Elecrow-RD/2-PACK-2.4inch-ESP32-Solo-Miner-LCD-Display/example/V1.0_A_green_circular_sticker_on_the_back/IDF_Code/DHT_screen_2.4_base/components/lvgl-3/docs/_static/img/js_calculator.gif

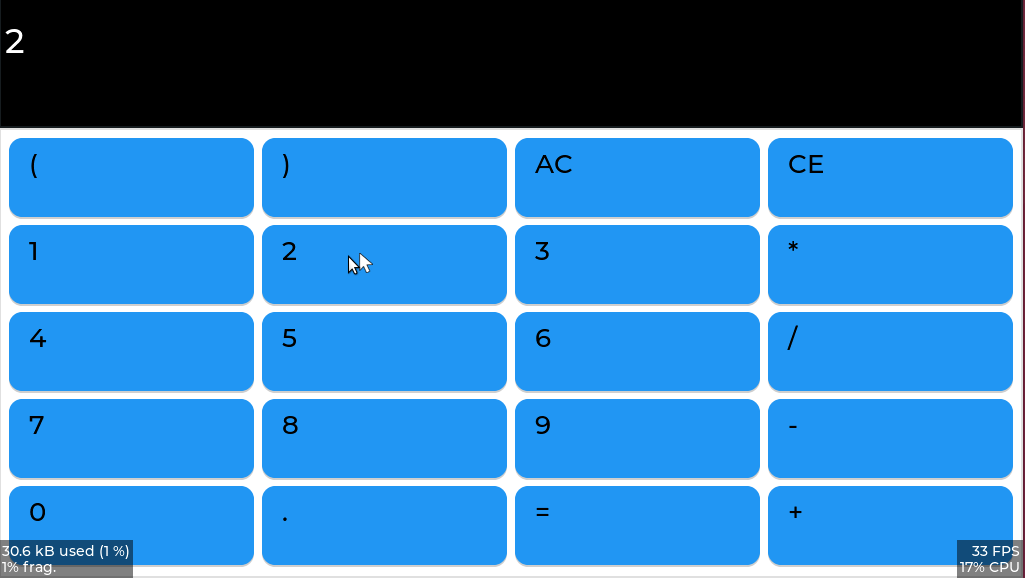
example/V1.0_A_green_circular_sticker_on_the_back/IDF_Code/DHT_screen_2.4_base/components/lvgl-3/docs/_static/img/js_calculator.gif
