Elecrow-RD/2-PACK-2.4inch-ESP32-Solo-Miner-LCD-Display/example/V1.0_A_green_circular_sticker_on_the_back/IDF_Code/DHT_screen_2.4_base/components/TFT_eSPI/examples/320 x 240/All_Free_Fonts_Demo/All_Free_Fonts_Demo.ino

/*
  Example for TFT_eSPI library

  Created by Bodmer 31/12/16

  This example draws all fonts (as used by the Adafruit_GFX library) onto the
  screen. These fonts are called the GFX Free Fonts (GFXFF) in this library.

  The fonts are referenced by a short name, see the Free_Fonts.h file
  attached to this sketch.

  Other True Type fonts could be converted using the utility within the
  "fontconvert" folder inside the library. This converted has also been
  copied from the Adafruit_GFX library. 

  Since these fonts are a recent addition Adafruit do not have a tutorial
  available yet on how to use the fontconvert utility.   Linux users will
  no doubt figure it out!  In the meantime there are 48 font files to use
  in sizes from 9 point to 24 point, and in normal, bold, and italic or
  oblique styles.

  This example sketch uses both the print class and drawString() functions
  to plot text to the screen.

  Make sure LOAD_GFXFF is defined in the User_Setup.h file within the
  library folder.

  --------------------------- NOTE ----------------------------------------
  The free font encoding format does not lend itself easily to plotting
  the background without flicker. For values that changes on screen it is
  better to use Fonts 1- 8 which are encoded specifically for rapid
  drawing with background.
  -------------------------------------------------------------------------

  #########################################################################
  ###### DON'T FORGET TO UPDATE THE User_Setup.h FILE IN THE LIBRARY ######
  ######       TO SELECT YOUR DISPLAY TYPE AND ENABLE FONTS          ######
  #########################################################################
*/

#define TEXT "aA MWyz~12" // Text that will be printed on screen in any font

#include "Free_Fonts.h" // Include the header file attached to this sketch

#include "SPI.h"
#include "TFT_eSPI.h"

// Use hardware SPI
TFT_eSPI tft = TFT_eSPI();

unsigned long drawTime = 0;

void setup(void) {

  tft.begin();

  tft.setRotation(1);

}

void loop() {

  // >>>>>>>>>>>>>>>>>>>>>>>>>>>>>>>>>>>>>>>>>>>>>>>>>>>>>>>>>>>>>>>>>>>>>>>>>>>>>>>>>
  // Show all 48 fonts in centre of screen ( x,y coordinate 160,120)
  // >>>>>>>>>>>>>>>>>>>>>>>>>>>>>>>>>>>>>>>>>>>>>>>>>>>>>>>>>>>>>>>>>>>>>>>>>>>>>>>>>

  // Where font sizes increase the screen is not cleared as the larger fonts overwrite
  // the smaller one with the background colour.

  // Set text datum to middle centre
  tft.setTextDatum(MC_DATUM);

  // Set text colour to orange with black background
  tft.setTextColor(TFT_WHITE, TFT_BLACK);
  
  tft.fillScreen(TFT_BLACK);            // Clear screen
  tft.setFreeFont(FF18);                 // Select the font
  tft.drawString(sFF1, 160, 60, GFXFF);// Print the string name of the font
  tft.setFreeFont(FF1);                 // Select the font
  tft.drawString(TEXT, 160, 120, GFXFF);// Print the string name of the font
  delay(1000);
  //tft.fillScreen(TFT_BLACK);
  tft.setFreeFont(FF18);                 // Select the font
  tft.drawString(sFF2, 160, 60, GFXFF);// Print the string name of the font
  tft.setFreeFont(FF2);
  tft.drawString(TEXT, 160, 120, GFXFF);
  delay(1000);
  //tft.fillScreen(TFT_BLACK);
  tft.setFreeFont(FF18);                 // Select the font
  tft.drawString(sFF3, 160, 60, GFXFF);// Print the string name of the font
  tft.setFreeFont(FF3);
  tft.drawString(TEXT, 160, 120, GFXFF);
  delay(1000);
  //tft.fillScreen(TFT_BLACK);
  tft.setFreeFont(FF18);                 // Select the font
  tft.drawString(sFF4, 160, 60, GFXFF);// Print the string name of the font
  tft.setFreeFont(FF4);
  tft.drawString(TEXT, 160, 120, GFXFF);
  delay(1000);
  
  tft.fillScreen(TFT_BLACK);
  tft.setFreeFont(FF18);                 // Select the font
  tft.drawString(sFF5, 160, 60, GFXFF);// Print the string name of the font
  tft.setFreeFont(FF5);
  tft.drawString(TEXT, 160, 120, GFXFF);
  delay(1000);
  //tft.fillScreen(TFT_BLACK);
  tft.setFreeFont(FF18);                 // Select the font
  tft.drawString(sFF6, 160, 60, GFXFF);// Print the string name of the font
  tft.setFreeFont(FF6);
  tft.drawString(TEXT, 160, 120, GFXFF);
  delay(1000);
  //tft.fillScreen(TFT_BLACK);
  tft.setFreeFont(FF18);                 // Select the font
  tft.drawString(sFF7, 160, 60, GFXFF);// Print the string name of the font
  tft.setFreeFont(FF7);
  tft.drawString(TEXT, 160, 120, GFXFF);
  delay(1000);
  //tft.fillScreen(TFT_BLACK);
  tft.setFreeFont(FF18);                 // Select the font
  tft.drawString(sFF8, 160, 60, GFXFF);// Print the string name of the font
  tft.setFreeFont(FF8);
  tft.drawString(TEXT, 160, 120, GFXFF);
  delay(1000);
  
  tft.fillScreen(TFT_BLACK);
  tft.setFreeFont(FF18);                 // Select the font
  tft.drawString(sFF9, 160, 60, GFXFF);// Print the string name of the font
  tft.setFreeFont(FF9);
  tft.drawString(TEXT, 160, 120, GFXFF);
  delay(1000);
  //tft.fillScreen(TFT_BLACK);
  tft.setFreeFont(FF18);                 // Select the font
  tft.drawString(sFF10, 160, 60, GFXFF);// Print the string name of the font
  tft.setFreeFont(FF10);
  tft.drawString(TEXT, 160, 120, GFXFF);
  delay(1000);
  //tft.fillScreen(TFT_BLACK);
  tft.setFreeFont(FF18);                 // Select the font
  tft.drawString(sFF11, 160, 60, GFXFF);// Print the string name of the font
  tft.setFreeFont(FF11);
  tft.drawString(TEXT, 160, 120, GFXFF);
  delay(1000);
  //tft.fillScreen(TFT_BLACK);
  tft.setFreeFont(FF18);                 // Select the font
  tft.drawString(sFF12, 160, 60, GFXFF);// Print the string name of the font
  tft.setFreeFont(FF12);
    tft.drawString(TEXT, 160, 120, GFXFF);
  delay(1000);
  
  tft.fillScreen(TFT_BLACK);
  tft.setFreeFont(FF18);                 // Select the font
  tft.drawString(sFF13, 160, 60, GFXFF);// Print the string name of the font
  tft.setFreeFont(FF13);
  tft.drawString(TEXT, 160, 120, GFXFF);
  delay(1000);
  //tft.fillScreen(TFT_BLACK);
  tft.setFreeFont(FF18);                 // Select the font
  tft.drawString(sFF14, 160, 60, GFXFF);// Print the string name of the font
  tft.setFreeFont(FF14);
  tft.drawString(TEXT, 160, 120, GFXFF);
  delay(1000);
  //tft.fillScreen(TFT_BLACK);
  tft.setFreeFont(FF18);                 // Select the font
  tft.drawString(sFF15, 160, 60, GFXFF);// Print the string name of the font
  tft.setFreeFont(FF15);
  tft.drawString(TEXT, 160, 120, GFXFF);
  delay(1000);
  //tft.fillScreen(TFT_BLACK);
  tft.setFreeFont(FF18);                 // Select the font
  tft.drawString(sFF16, 160, 60, GFXFF);// Print the string name of the font
  tft.setFreeFont(FF16);
    tft.drawString(TEXT, 160, 120, GFXFF);
  delay(1000);
  
  tft.fillScreen(TFT_BLACK);
  tft.setFreeFont(FF18);                 // Select the font
  tft.drawString(sFF17, 160, 60, GFXFF);// Print the string name of the font
  tft.setFreeFont(FF17);
  tft.drawString(TEXT, 160, 120, GFXFF);
  delay(1000);
  //tft.fillScreen(TFT_BLACK);
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
  delay(1000);
  //tft.fillScreen(TFT_BLACK);
  tft.setFreeFont(FF18);                 // Select the font
  tft.drawString(sFF47, 160, 60, GFXFF);// Print the string name of the font
  tft.setFreeFont(FF47);
  tft.drawString(TEXT, 160, 120, GFXFF);
  delay(1000);
  //tft.fillScreen(TFT_BLACK);
  tft.setFreeFont(FF18);                 // Select the font
  tft.drawString(sFF48, 160, 60, GFXFF);// Print the string name of the font
  tft.setFreeFont(FF48);
  tft.drawString(TEXT, 160, 120, GFXFF);
  delay(1000);

}

// There follows a crude way of flagging that this example sketch needs fonts which
// have not been enbabled in the User_Setup.h file inside the TFT_HX8357 library.
//
// These lines produce errors during compile time if settings in User_Setup are not correct
//
// The error will be "does not name a type" but ignore this and read the text between ''
// it will indicate which font or feature needs to be enabled
//
// Either delete all the following lines if you do not want warnings, or change the lines
// to suit your sketch modifications.

#ifndef LOAD_GLCD
//ERROR_Please_enable_LOAD_GLCD_in_User_Setup
#endif

#ifndef LOAD_GFXFF
ERROR_Please_enable_LOAD_GFXFF_in_User_Setup!
#endif
