Elecrow-RD/2-PACK-2.4inch-ESP32-Solo-Miner-LCD-Display/example/V1.0_A_green_circular_sticker_on_the_back/IDF_Code/DHT_screen_2.4_base/components/arduino-esp32-master/cores/esp32/HardwareSerial.h

/*
 HardwareSerial.h - Hardware serial library for Wiring
 Copyright (c) 2006 Nicholas Zambetti.  All right reserved.

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
 Modified 28 September 2010 by Mark Sproul
 Modified 14 August 2012 by Alarus
 Modified 3 December 2013 by Matthijs Kooijman
 Modified 18 December 2014 by Ivan Grokhotkov (esp8266 platform support)
 Modified 31 March 2015 by Markus Sattler (rewrite the code for UART0 + UART1 support in ESP8266)
 Modified 25 April 2015 by Thomas Flayols (add configuration different from 8N1 in ESP8266)
 Modified 13 October 2018 by Jeroen Döll (add baudrate detection)
 Baudrate detection example usage (detection on Serial1):
   void setup() {
     Serial.begin(115200);
     delay(100);
     Serial.println();

     Serial1.begin(0, SERIAL_8N1, -1, -1, true, 11000UL);  // Passing 0 for baudrate to detect it, the last parameter is a timeout in ms

     unsigned long detectedBaudRate = Serial1.baudRate();
     if(detectedBaudRate) {
       Serial.printf("Detected baudrate is %lu\n", detectedBaudRate);
     } else {
       Serial.println("No baudrate detected, Serial1 will not work!");
     }
   }

 Pay attention: the baudrate returned by baudRate() may be rounded, eg 115200 returns 115201
 */

#ifndef HardwareSerial_h
#define HardwareSerial_h

#include <inttypes.h>
#include <functional>
#include "Stream.h"
#include "esp32-hal.h"
#include "soc/soc_caps.h"
#include "HWCDC.h"

#include "freertos/FreeRTOS.h"
#include "freertos/task.h"
#include "freertos/semphr.h"

typedef enum {
    UART_BREAK_ERROR,
    UART_BUFFER_FULL_ERROR,
    UART_FIFO_OVF_ERROR,
    UART_FRAME_ERROR,
    UART_PARITY_ERROR
} hardwareSerial_error_t;

typedef std::function<void(void)> OnReceiveCb;
typedef std::function<void(hardwareSerial_error_t)> OnReceiveErrorCb;

class HardwareSerial: public Stream
{
public:
    HardwareSerial(int uart_nr);
    ~HardwareSerial();

    // setRxTimeout sets the timeout after which onReceive callback will be called (after receiving data, it waits for this time of UART rx inactivity to call the callback fnc)
    // param symbols_timeout defines a timeout threshold in uart symbol periods. Setting 0 symbol timeout disables the callback call by timeout.
    //                       Maximum timeout setting is calculacted automatically by IDF. If set above the maximum, it is ignored and an error is printed on Serial0 (check console).
    //                       Examples: Maximum for 11 bits symbol is 92 (SERIAL_8N2, SERIAL_8E1, SERIAL_8O1, etc), Maximum for 10 bits symbol is 101 (SERIAL_8N1).
    //                       For example symbols_timeout=1 defines a timeout equal to transmission time of one symbol (~11 bit) on current baudrate. 
    //                       For a baudrate of 9600, SERIAL_8N1 (10 bit symbol) and symbols_timeout = 3, the timeout would be 3 / (9600 / 10) = 3.125 ms
    void setRxTimeout(uint8_t symbols_timeout);

    // onReceive will setup a callback that will be called whenever an UART interruption occurs (UART_INTR_RXFIFO_FULL or UART_INTR_RXFIFO_TOUT)
    // UART_INTR_RXFIFO_FULL interrupt triggers at UART_FULL_THRESH_DEFAULT bytes received (defined as 120 bytes by default in IDF)
    // UART_INTR_RXFIFO_TOUT interrupt triggers at UART_TOUT_THRESH_DEFAULT symbols passed without any reception (defined as 10 symbos by default in IDF)
    // onlyOnTimeout parameter will define how onReceive will behave:
    // Default: true -- The callback will only be called when RX Timeout happens. 
    //                  Whole stream of bytes will be ready for being read on the callback function at once.
    //                  This option may lead to Rx Overflow depending on the Rx Buffer Size and number of bytes received in the streaming
    //         false -- The callback will be called when FIFO reaches 120 bytes and also on RX Timeout.
    //                  The stream of incommig bytes will be "split" into blocks of 120 bytes on each callback.
    //                  This option avoid any sort of Rx Overflow, but leaves the UART packet reassembling work to the Application.
    void onReceive(OnReceiveCb function, bool onlyOnTimeout = true);

    // onReceive will be called on error events (see hardwareSerial_error_t)
    void onReceiveError(OnReceiveErrorCb function);

    // eventQueueReset clears all events in the queue (the events that trigger onReceive and onReceiveError) - maybe usefull in some use cases
    void eventQueueReset();
 
    void begin(unsigned long baud, uint32_t config=SERIAL_8N1, int8_t rxPin=-1, int8_t txPin=-1, bool invert=false, unsigned long timeout_ms = 20000UL, uint8_t rxfifo_full_thrhd = 112);
    void end(bool fullyTerminate = true);
    void updateBaudRate(unsigned long baud);
    int available(void);
    int availableForWrite(void);
    int peek(void);
    int read(void);
    size_t read(uint8_t *buffer, size_t size);
    inline size_t read(char * buffer, size_t size)
    {
        return read((uint8_t*) buffer, size);
    }
    void flush(void);
    void flush( bool txOnly);
    size_t write(uint8_t);
    size_t write(const uint8_t *buffer, size_t size);
    inline size_t write(const char * buffer, size_t size)
    {
        return write((uint8_t*) buffer, size);
    }
    inline size_t write(const char * s)
    {
        return write((uint8_t*) s, strlen(s));
    }
    inline size_t write(unsigned long n)
    {
        return write((uint8_t) n);
    }
    inline size_t write(long n)
    {
        return write((uint8_t) n);
    }
    inline size_t write(unsigned int n)
    {
        return write((uint8_t) n);
    }
    inline size_t write(int n)
    {
        return write((uint8_t) n);
    }
    uint32_t baudRate();
    operator bool() const;

    void setDebugOutput(bool);
    
    void setRxInvert(bool);

    // Negative Pin Number will keep it unmodified, thus this function can set individual pins
    // SetPins shall be called after Serial begin()
    void setPins(int8_t rxPin, int8_t txPin, int8_t ctsPin = -1, int8_t rtsPin = -1);
    // Enables or disables Hardware Flow Control using RTS and/or CTS pins (must use setAllPins() before)
    void setHwFlowCtrlMode(uint8_t mode = HW_FLOWCTRL_CTS_RTS, uint8_t threshold = 64);   // 64 is half FIFO Length

    size_t setRxBufferSize(size_t new_size);
    size_t setTxBufferSize(size_t new_size);

protected:
    int _uart_nr;
    uart_t* _uart;
    size_t _rxBufferSize;
    size_t _txBufferSize;
    OnReceiveCb _onReceiveCB;
    OnReceiveErrorCb _onReceiveErrorCB;
    // _onReceive and _rxTimeout have be consistent when timeout is disabled
    bool _onReceiveTimeout;
    uint8_t _rxTimeout;
    TaskHandle_t _eventTask;
#if !CONFIG_DISABLE_HAL_LOCKS
    SemaphoreHandle_t _lock;
#endif

    void _createEventTask(void *args);
    void _destroyEventTask(void);
    static void _uartEventTask(void *args);
};

extern void serialEventRun(void) __attribute__((weak));

#if !defined(NO_GLOBAL_INSTANCES) && !defined(NO_GLOBAL_SERIAL)
#ifndef ARDUINO_USB_CDC_ON_BOOT
#define ARDUINO_USB_CDC_ON_BOOT 0
#endif
#if ARDUINO_USB_CDC_ON_BOOT //Serial used for USB CDC
#if !ARDUINO_USB_MODE
#include "USB.h"
#include "USBCDC.h"
#endif
extern HardwareSerial Serial0;
#else
extern HardwareSerial Serial;
#endif
#if SOC_UART_NUM > 1
extern HardwareSerial Serial1;
#endif
#if SOC_UART_NUM > 2
extern HardwareSerial Serial2;
#endif
#endif

#endif // HardwareSerial_h
