Elecrow-RD/2-PACK-2.4inch-ESP32-Solo-Miner-LCD-Display/example/V1.0_A_green_circular_sticker_on_the_back/IDF_Code/DHT_screen_2.4_base/components/arduino-esp32-master/variants/adafruit_magtag29_esp32s2/pins_arduino.h

#ifndef Pins_Arduino_h
#define Pins_Arduino_h

#include <stdint.h>


#define USB_VID            0x239A
#define USB_PID            0x80E5
#define USB_MANUFACTURER   "Adafruit"
#define USB_PRODUCT        "EPD MagTag 2.9\" ESP32-S2"
#define USB_SERIAL         "" // Empty string for MAC adddress


#define EXTERNAL_NUM_INTERRUPTS 46
#define NUM_DIGITAL_PINS        48
#define NUM_ANALOG_INPUTS       20

#define analogInputToDigitalPin(p)  (((p)<20)?(analogChannelToDigitalPin(p)):-1)
#define digitalPinToInterrupt(p)    (((p)<48)?(p):-1)
#define digitalPinHasPWM(p)         (p < 46)

#define LED_BUILTIN         13

#define PIN_NEOPIXEL        1    // D1
#define NEOPIXEL_NUM        4    // number of neopixels
#define NEOPIXEL_POWER      21   // power pin
#define NEOPIXEL_POWER_ON   LOW  // power pin state when on


#define PIN_BUTTON1         15
#define PIN_BUTTON2         14
#define PIN_BUTTON3         12
#define PIN_BUTTON4         11
#define PIN_BUTTON5         0  // BOOT0 switch

static const uint8_t EPD_BUSY  = 5;
static const uint8_t EPD_RESET = 6;
static const uint8_t EPD_DC    = 7;
static const uint8_t EPD_CS    = 8;

static const uint8_t ACCEL_IRQ = 9;

static const uint8_t BUTTON_A = PIN_BUTTON1;
static const uint8_t BUTTON_B = PIN_BUTTON2;
static const uint8_t BUTTON_C = PIN_BUTTON3;
static const uint8_t BUTTON_D = PIN_BUTTON4;

static const uint8_t LIGHT_SENSOR = 3;
static const uint8_t BATT_MONITOR = 4;
static const uint8_t SPEAKER_SHUTDOWN = 16;

static const uint8_t SDA = 33;
static const uint8_t SCL = 34;

static const uint8_t SS    = 8;
static const uint8_t MOSI  = 35;
static const uint8_t SCK   = 36;
static const uint8_t MISO  = 37;





static const uint8_t TX = 43;
static const uint8_t RX = 44;


static const uint8_t A0 = 17;
static const uint8_t A1 = 18;
static const uint8_t A2 = 1;
static const uint8_t A3 = 2;
static const uint8_t A4 = 3;
static const uint8_t A5 = 4;
static const uint8_t A6 = 5;
static const uint8_t A7 = 6;
static const uint8_t A8 = 7;
static const uint8_t A9 = 8;
static const uint8_t A10 = 9;
static const uint8_t A11 = 10;
static const uint8_t A12 = 11;
static const uint8_t A13 = 12;
static const uint8_t A14 = 13;
static const uint8_t A15 = 14;
static const uint8_t A16 = 15;
static const uint8_t A17 = 16;
static const uint8_t A18 = 19;
static const uint8_t A19 = 20;


static const uint8_t T10 = 10;


static const uint8_t DAC1 = 17;
static const uint8_t DAC2 = 18;

#endif /* Pins_Arduino_h */
