Elecrow-RD/2-PACK-2.4inch-ESP32-Solo-Miner-LCD-Display/example/V1.0_A_green_circular_sticker_on_the_back/IDF_Code/DHT_screen_2.4_base/components/arduino-esp32-master/variants/adafruit_feather_esp32s2/pins_arduino.h

#ifndef Pins_Arduino_h
#define Pins_Arduino_h

#include <stdint.h>


#define USB_VID            0x239A
#define USB_PID            0x80EB
#define USB_MANUFACTURER   "Adafruit"
#define USB_PRODUCT        "Feather ESP32-S2"
#define USB_SERIAL         "" // Empty string for MAC adddress


#define EXTERNAL_NUM_INTERRUPTS 46
#define NUM_DIGITAL_PINS        48
#define NUM_ANALOG_INPUTS       20

#define analogInputToDigitalPin(p)  (((p)<20)?(analogChannelToDigitalPin(p)):-1)
#define digitalPinToInterrupt(p)    (((p)<48)?(p):-1)
#define digitalPinHasPWM(p)         (p < 46)

#define LED_BUILTIN     13

#define PIN_NEOPIXEL        33
#define NEOPIXEL_NUM        1     // number of neopixels
#define NEOPIXEL_POWER      21    // power pin
#define NEOPIXEL_POWER_ON   HIGH  // power pin state when on
#define I2C_POWER           7     // I2C power pin
#define PIN_I2C_POWER       7     // I2C power pin

static const uint8_t SDA = 3;
static const uint8_t SCL = 4;

static const uint8_t SS    = 42;
static const uint8_t MOSI  = 35;
static const uint8_t SCK   = 36;
static const uint8_t MISO  = 37;

static const uint8_t A0 = 18;
static const uint8_t A1 = 17;
static const uint8_t A2 = 16;
static const uint8_t A3 = 15;
static const uint8_t A4 = 14;
static const uint8_t A5 = 8;


static const uint8_t TX = 39;
static const uint8_t RX = 38;
#define TX1 TX
#define RX1 RX

static const uint8_t T5 = 5;
static const uint8_t T6 = 6;
static const uint8_t T8 = 8;
static const uint8_t T9 = 9;
static const uint8_t T10 = 10;
static const uint8_t T11 = 11;
static const uint8_t T12 = 12;
static const uint8_t T13 = 13;
static const uint8_t T14 = 14;

static const uint8_t DAC1 = 17;
static const uint8_t DAC2 = 18;

#endif /* Pins_Arduino_h */
