Elecrow-RD/2-PACK-2.4inch-ESP32-Solo-Miner-LCD-Display/example/V1.0_A_green_circular_sticker_on_the_back/IDF_Code/DHT_screen_2.4_base/components/arduino-esp32-master/variants/bpi-bit/pins_arduino.h

#ifndef Pins_Arduino_h
#define Pins_Arduino_h

#include <stdint.h>

#define EXTERNAL_NUM_INTERRUPTS 16
#define NUM_DIGITAL_PINS 40
#define NUM_ANALOG_INPUTS 16

#define analogInputToDigitalPin(p) (((p) < 20) ? (analogChannelToDigitalPin(p)) : -1)
#define digitalPinToInterrupt(p) (((p) < 40) ? (p) : -1)
#define digitalPinHasPWM(p) (p < 34)

static const uint8_t BUZZER = 25;

static const uint8_t BUTTON_A = 35;
static const uint8_t BUTTON_B = 27;

static const uint8_t RGB_LED = 4;

static const uint8_t LIGHT_SENSOR1 = 36;
static const uint8_t LIGHT_SENSOR2 = 39;

static const uint8_t TEMPERATURE_SENSOR = 34;

static const uint8_t MPU9250_INT = 0;

static const uint8_t TX = 1;
static const uint8_t RX = 3;

static const uint8_t SDA = 21;
static const uint8_t SCL = 22;

static const uint8_t SS = 5;
static const uint8_t MOSI = 23;
static const uint8_t MISO = 19;
static const uint8_t SCK = 18;

static const uint8_t P0 = 25;
static const uint8_t P1 = 32;
static const uint8_t P2 = 33;
static const uint8_t P3 = 13;
static const uint8_t P4 = 15;
static const uint8_t P5 = 35;
static const uint8_t P6 = 12;
static const uint8_t P7 = 14;
static const uint8_t P8 = 16;
static const uint8_t P9 = 17;
static const uint8_t P10 = 26;
static const uint8_t P11 = 27;
static const uint8_t P12 = 2;
static const uint8_t P13 = 18;
static const uint8_t P14 = 19;
static const uint8_t P15 = 23;
static const uint8_t P16 = 5;
static const uint8_t P19 = 22;
static const uint8_t P20 = 21;

static const uint8_t DAC1 = 25;
static const uint8_t DAC2 = 26;

#endif /* Pins_Arduino_h */
