Elecrow-RD/2-PACK-2.4inch-ESP32-Solo-Miner-LCD-Display/example/V1.0_A_green_circular_sticker_on_the_back/IDF_Code/DHT_screen_2.4_base/components/arduino-esp32-master/variants/esp32-poe-iso/pins_arduino.h

#ifndef Pins_Arduino_h
#define Pins_Arduino_h

#include <stdint.h>

#define EXTERNAL_NUM_INTERRUPTS 16
#define NUM_DIGITAL_PINS        40
#define NUM_ANALOG_INPUTS       16

#define analogInputToDigitalPin(p)  (((p)<20)?(analogChannelToDigitalPin(p)):-1)
#define digitalPinToInterrupt(p)    (((p)<40)?(p):-1)
#define digitalPinHasPWM(p)         (p < 34)

#define ETH_CLK_MODE ETH_CLOCK_GPIO17_OUT
#define ETH_PHY_POWER 12

static const uint8_t KEY_BUILTIN = 34;

static const uint8_t TX = 1;
static const uint8_t RX = 3;

#define TX1 4
#define RX1 36

#define TX2 33	// ext2 pin 5
#define RX2 35	// ext2 pin 3

static const uint8_t SDA = 13;
static const uint8_t SCL = 16;

static const uint8_t SS    = 5;
static const uint8_t MOSI  = 2;
static const uint8_t MISO  = 15;
static const uint8_t SCK   = 14;

#define BOARD_HAS_1BIT_SDMMC

#endif /* Pins_Arduino_h */
