Elecrow-RD/2-PACK-2.4inch-ESP32-Solo-Miner-LCD-Display/example/V1.0_A_green_circular_sticker_on_the_back/IDF_Code/DHT_screen_2.4_base/components/arduino-esp32-master/variants/m5stack_atom/pins_arduino.h

#ifndef Pins_Arduino_h
#define Pins_Arduino_h

#include <stdint.h>

#define EXTERNAL_NUM_INTERRUPTS 16
#define NUM_DIGITAL_PINS        40
#define NUM_ANALOG_INPUTS       16

#define analogInputToDigitalPin(p)  (((p)<20)?(analogChannelToDigitalPin(p)):-1)
#define digitalPinToInterrupt(p)    (((p)<40)?(p):-1)
#define digitalPinHasPWM(p)         (p < 34)

static const uint8_t TX = 1;
static const uint8_t RX = 3;

static const uint8_t SDA = 26;
static const uint8_t SCL = 32;


static const uint8_t G12 = 12;
static const uint8_t G19 = 19;
static const uint8_t G21 = 21;
static const uint8_t G22 = 22;
static const uint8_t G23 = 23;
static const uint8_t G25 = 25;
static const uint8_t G26 = 26;
static const uint8_t G27 = 27;
static const uint8_t G32 = 32;
static const uint8_t G33 = 33;
static const uint8_t G39 = 39;

static const uint8_t G9 = 9;
static const uint8_t G10 = 10;
static const uint8_t G37 = 37;
static const uint8_t G36 = 36;
static const uint8_t G0 = 0;

static const uint8_t DAC1 = 25;
static const uint8_t DAC2 = 26;

static const uint8_t ADC1 = 35;
static const uint8_t ADC2 = 36;

static const uint8_t SS    = 19;
static const uint8_t MOSI  = 33;
static const uint8_t MISO  = 23;
static const uint8_t SCK   = 22;

#endif /* Pins_Arduino_h */
