Elecrow-RD/2-PACK-2.4inch-ESP32-Solo-Miner-LCD-Display/example/V1.0_A_green_circular_sticker_on_the_back/IDF_Code/DHT_screen_2.4_base/components/TFT_eSPI/examples/Smooth Graphics/Smooth_Graphics_Demo/Smooth_Graphics_Demo.ino

// Sketch to demonstrate smooth (anti-aliased) graphics funtions:
// Smooth graphics result in less pixel resolution jaggedness.

#include <TFT_eSPI.h> // Master copy here: https://github.com/Bodmer/TFT_eSPI

TFT_eSPI tft = TFT_eSPI();  // Invoke library, pins defined in User_Setup.h

TFT_eSprite spr = TFT_eSprite(&tft);

// =========================================================================
// Setup
// =========================================================================
void setup() {
  Serial.begin(115200);
  Serial.println("Booting...");

  // Initialise the screen
  tft.init();

  // Ideally set orientation for good viewing angle range because
  // the anti-aliasing effectiveness varies with screen viewing angle
  tft.setRotation(0);

  tft.fillScreen(TFT_BLACK);

  // Small sprite for spot demo
  spr.createSprite(23, 23);
}

// =========================================================================
// Loop
// =========================================================================
void loop() {

  // drawSpot is for small anti-aliased circles, coordinates and radius are
  // floating point to allow sub-pixel positioning (large circles will
  // be slow to draw). Use fillSmoothCircle() for large circles.
  // In this case black is the backgorund colour for the anti-aliasing
  float x = 10.5;
  float y = 10.5;
  float r = 8.6;
  tft.drawSpot(x, y, r, TFT_WHITE, TFT_BLACK);

  // Fill sprite with a colour
  spr.fillSprite(TFT_RED);
  // Draw spot in sprite, the backgorund colour is ommitted so function
  // reads background colour for aliasing. (To use this method with direct write
  // to TFT (tft.drawSpot...) requires the capability to read data from the TFT!)
  spr.drawSpot(x, y, r, TFT_WHITE);
  spr.pushSprite(21, 0);


  // Draw a segmented ring meter type display
  // Centre of screen
  int cx = tft.width()  / 2;
  int cy = tft.height() / 2;
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
